wntrblm/Neptune/factory/references/cv-fm1-neg.png

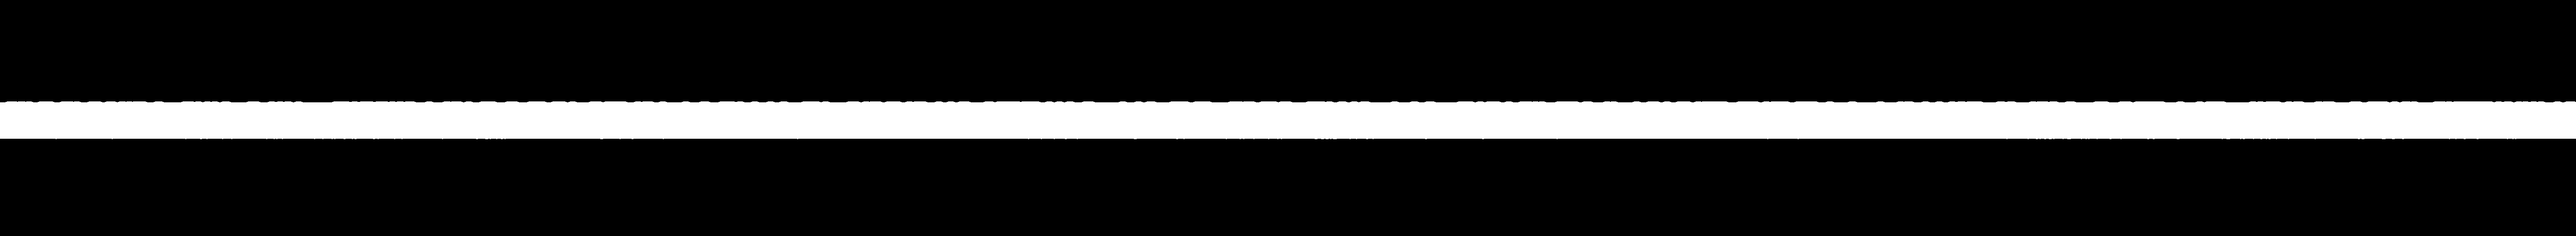
factory/references/cv-fm1-neg.png
