wntrblm/Neptune/factory/references/cv-fm1-pos.png

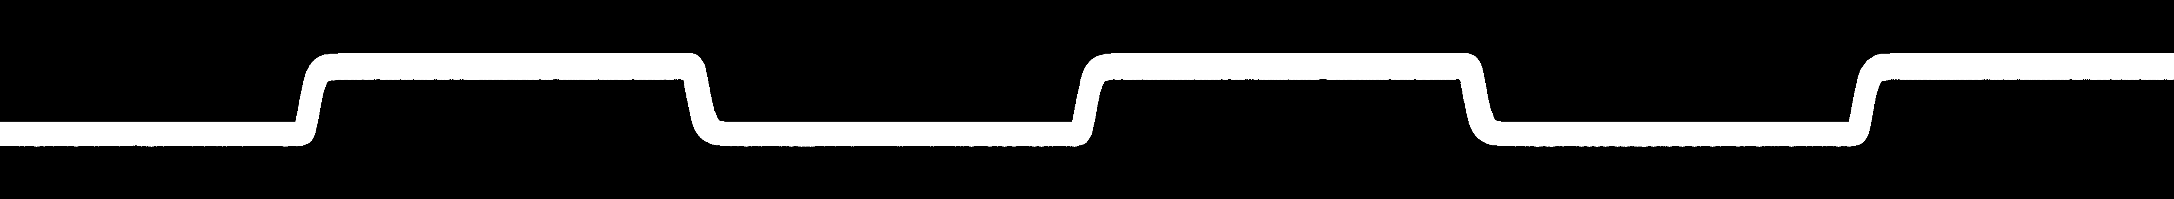
factory/references/cv-fm1-pos.png
