wntrblm/Neptune/factory/references/knob-hp-center.png

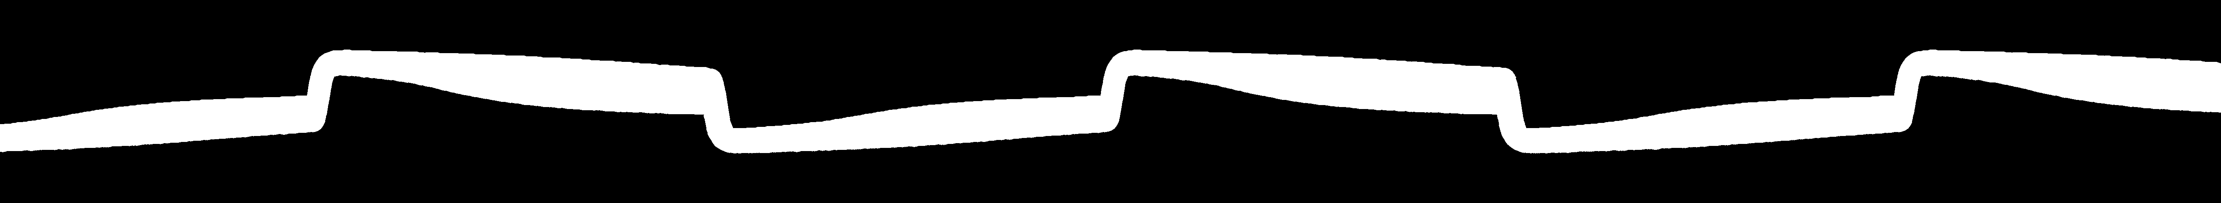
factory/references/knob-hp-center.png
