wntrblm/Neptune/factory/references/knob-hp-closed.png

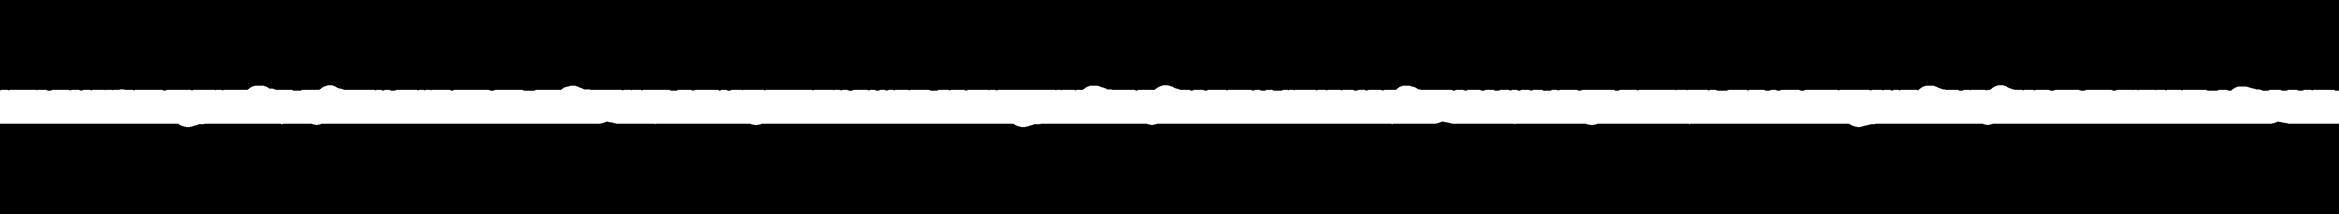
factory/references/knob-hp-closed.png
