wntrblm/Neptune/factory/references/knob-lp-center.png

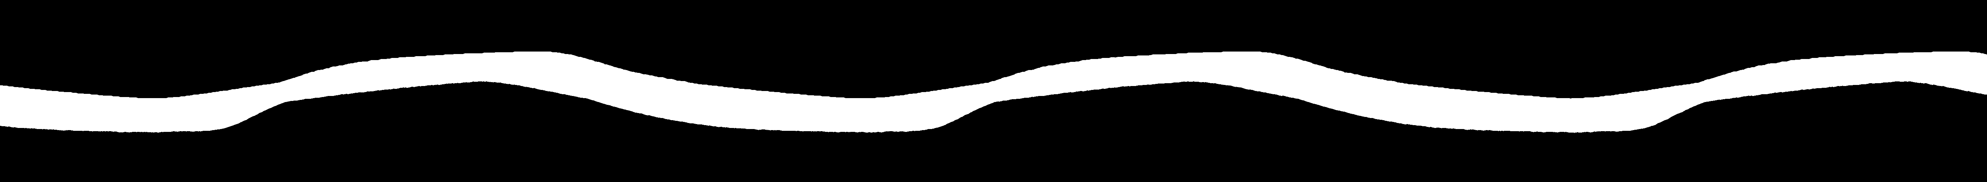
factory/references/knob-lp-center.png
