wntrblm/Neptune/factory/references/knob-lp-closed.png

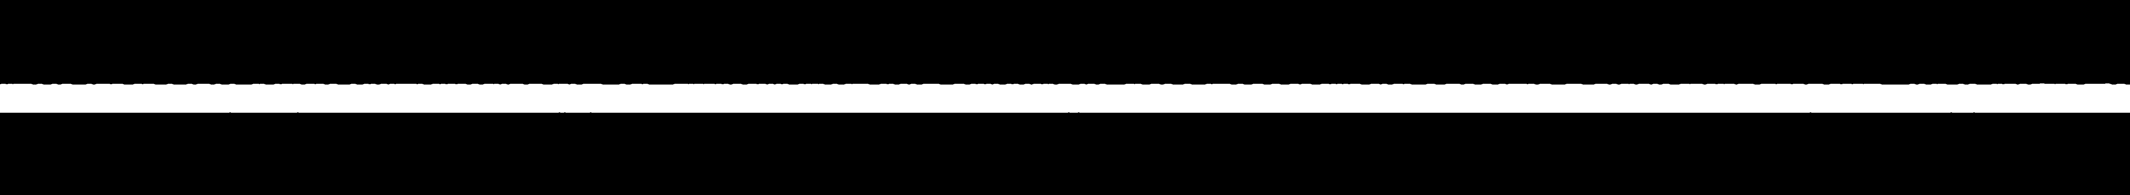
factory/references/knob-lp-closed.png
