wntrblm/Neptune/user_guide/docs/images/kit/0-kit-contents.webp

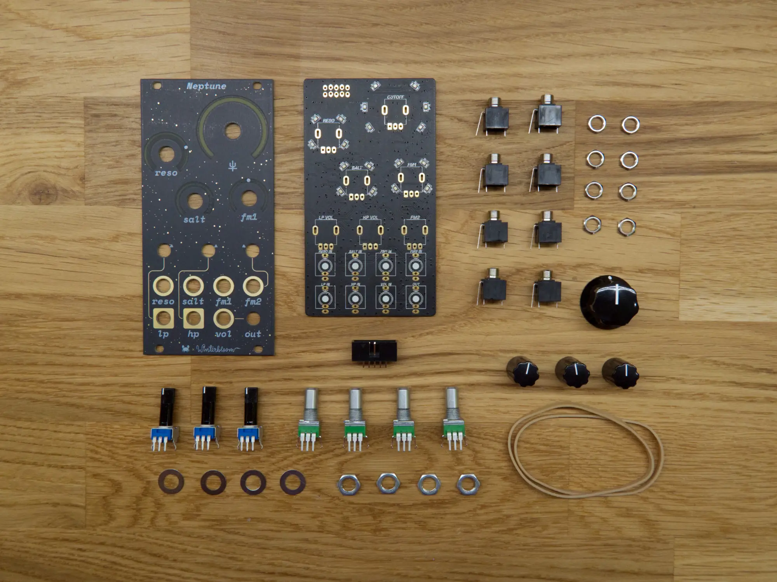
user_guide/docs/images/kit/0-kit-contents.webp
